mam1/Pcon-TNG/vendor_docs/BBB system Reference/preview-web.jpg

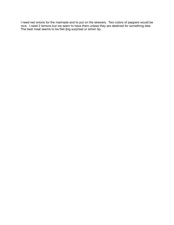
vendor_docs/BBB system Reference/preview-web.jpg
