mam1/Pcon-TNG/BBB/include/list_maint.h

#ifndef _LIST_MAINT_H_
#define _LIST_MAINT_H_

void del_elm(int *array_start, int *index, int value, int array_size);
void add_elm(int *array_start, int *index, int value, int array_size);


#endif // _LIST_MAINT_H_
