mam1/Pcon-TNG/BBB/include/Dcon.h

#ifndef DCONH_
#define DCONH_

/* Dcon version info */
#define _MAJOR_VERSION_Dcon		5
#define _MINOR_VERSION_Dcon 	0
#define _MINOR_REVISION_Dcon	0

#include "shared.h"


int count(void);
int dispevars(void);

#endif /* DCONH_ */
