mam1/Pcon-TNG/ESPSDK/t1.c

#include "ets_sys.h"
#include "osapi.h"
#include "gpio.h"
#include "os_type.h"
#include "user_interface.h"

// // ESP-12 modules have LED on GPIO2. Change to another GPIO
// // for other boards.
// static const int pin = 2;
// static volatile os_timer_t some_timer;

// void some_timerfunc(void *arg)
// {
//   //Do blinky stuff
//   if (GPIO_REG_READ(GPIO_OUT_ADDRESS) & (1 << pin))
//   {
//     // set gpio low
//     gpio_output_set(0, (1 << pin), 0, 0);
//   }
//   else
//   {
//     // set gpio high
//     gpio_output_set((1 << pin), 0, 0, 0);
//   }
// }

// void ICACHE_FLASH_ATTR user_init()
// {
//   // init gpio subsytem
//   gpio_init();

//   // configure UART TXD to be GPIO1, set as output
//   PIN_FUNC_SELECT(PERIPHS_IO_MUX_U0TXD_U, FUNC_GPIO1); 
//   gpio_output_set(0, 0, (1 << pin), 0);

//   // setup timer (500ms, repeating)
//   os_timer_setfn(&some_timer, (os_timer_func_t *)some_timerfunc, NULL);
//   os_timer_arm(&some_timer, 500, 1);
// }



// void sdk_init_done_cb(void) {
// const char ssid[32] = "my_home_ssid";
// const char password[32] = "my_home_password";

// struct station_config stationConf;

// wifi_set_opmode( STATION_MODE );
// os_memcpy(&stationConf.ssid, ssid, 32);
// os_memcpy(&stationConf.password, password, 32);
// wifi_station_set_config(&stationConf);
// wifi_station_connect();
// }

os_timer_t start_timer; /* declare a variable which will be used to control the timer */

void start_timer_cb(void *arg) { /* callback function for timer */
 static int on = 0;
 if (!on) { /* if LED is OFF - turn it on */
  gpio_output_set(BIT16, 0, BIT16, 0);
  on = 1;
 } else { /* if LED is ON - turn is off */
  gpio_output_set(0, BIT12, BIT12, 0);
  on = 0;
 }
}

void sdk_init_done_cb(void) {
// const char ssid[32] = "my_home_ssid";
// const char password[32] = "FrontierHSI";
// const char hostname[32] = "sensor-masters";
// struct station_config stationConf;
// wifi_set_opmode( STATION_MODE );
// os_memcpy(&stationConf.ssid, ssid, 32);
// os_memcpy(&stationConf.password, password, 32);
// wifi_station_set_config(&stationConf);
// wifi_station_connect();

 os_timer_disarm(&start_timer); 
 os_timer_setfn(&start_timer, start_timer_cb, NULL); /* Set callback for timer */
 os_timer_arm(&start_timer, 5000 /* call every 5 second */, 1 /* repeat */);
}
 
void user_init() {
 system_init_done_cb(sdk_init_done_cb);
}
