mam1/Pcon-TNG/BBB/include/char_fsm.h

/**************************************************/
/*                                                */
/*  header file for char_fsm.c                    */
/*                                                */
/**************************************************/

#ifndef CHAR_FSM_H_
#define CHAR_FSM_H_

/* char_fsm.c version */
#define _MAJOR_VERSION_char_fsm		10
#define _MINOR_VERSION_char_fsm		4
#define _MINOR_REVISION_char_fsm	0

/* data structures */
typedef struct node {
	struct node *next;
	char *tptr;
} TQ;


/* fuctions */
int char_fsm_reset(void);
void char_fsm(int, int *, char *);

int char_type(char);
int pop_cmd_q(char *);
int test_cmd_q();
TQ *process_buffer(void);

#endif
